JamesTwallin/gas_sensor/hardware/phone_board_mems/preview/phone_board_mems-F_Silkscreen.pdf

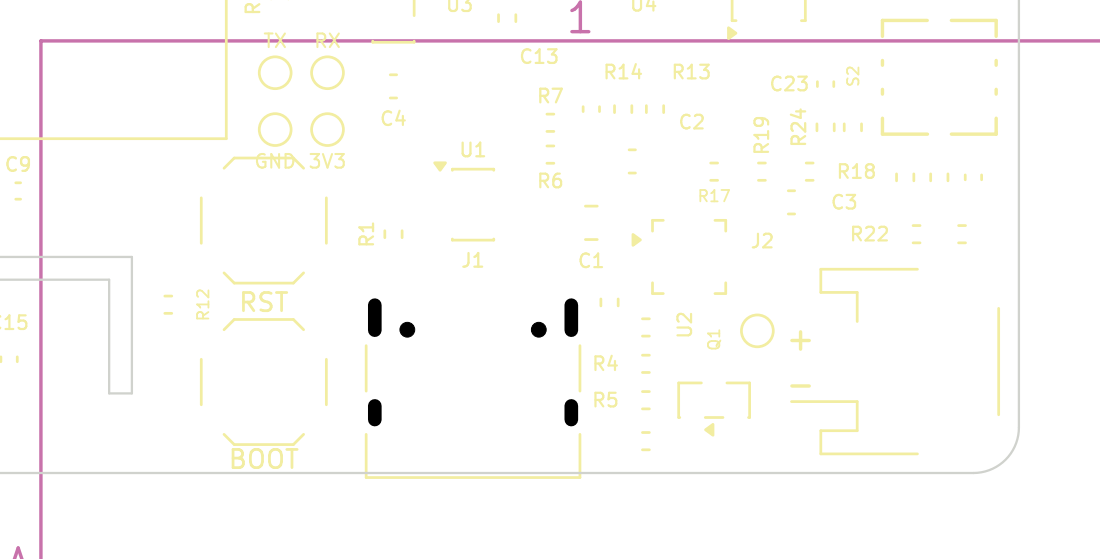
[picture p29: page 1]

Id: 5/7 Title: File: phone_board_mems.kicad_pcb Sheet:
