JamesTwallin/gas_sensor/hardware/phone_board_mems/preview/phone_board_mems-In1_Cu.pdf

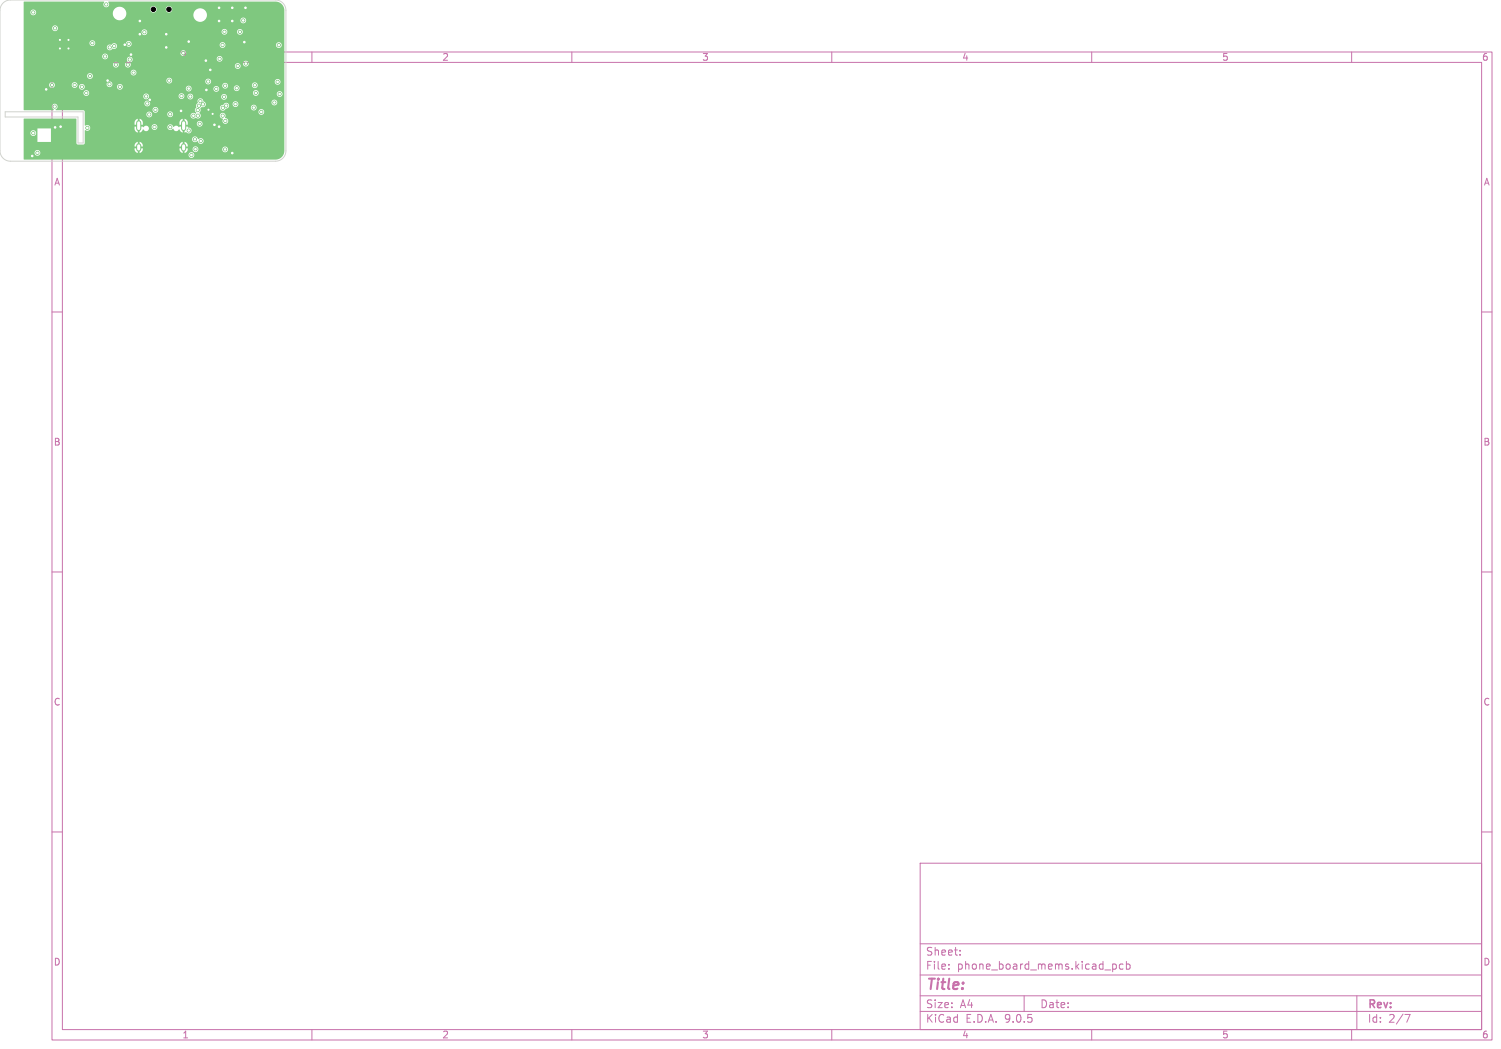
[picture p30: page 1]

Id: 2/7 Title: File: phone_board_mems.kicad_pcb Sheet:
