JamesTwallin/gas_sensor/hardware/phone_board_mems/preview/phone_board_mems-In2_Cu.pdf

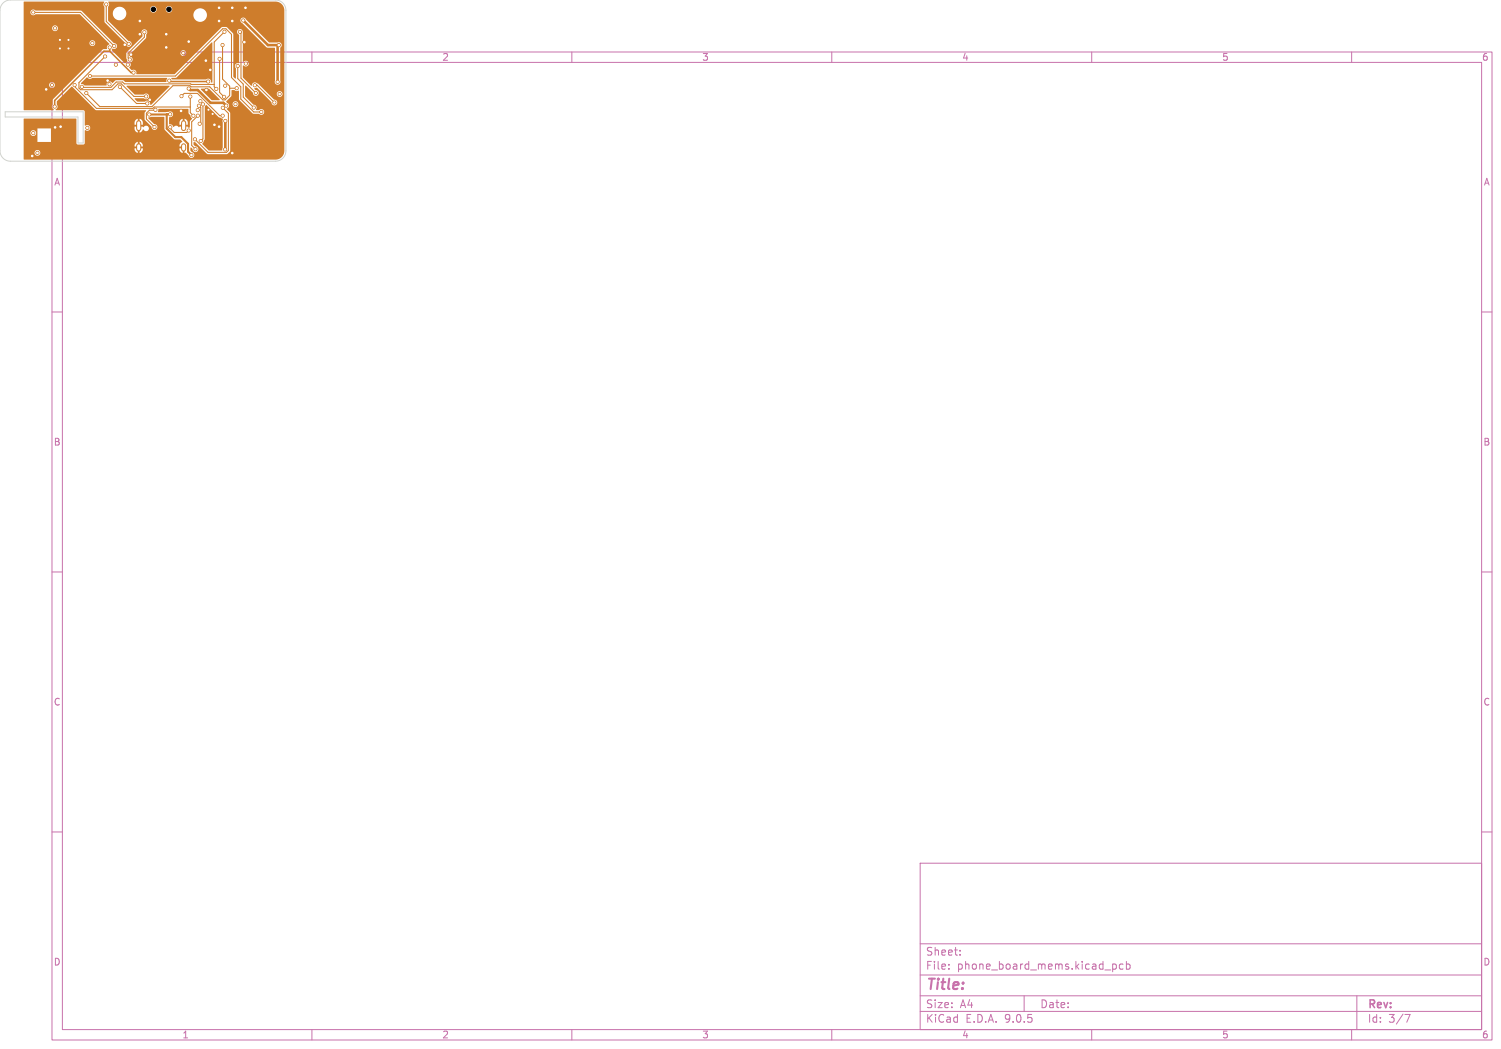
[picture p31: page 1]

Id: 3/7 Title: File: phone_board_mems.kicad_pcb Sheet:
