JamesTwallin/gas_sensor/hardware/phone_board_mems/preview/schematic.pdf

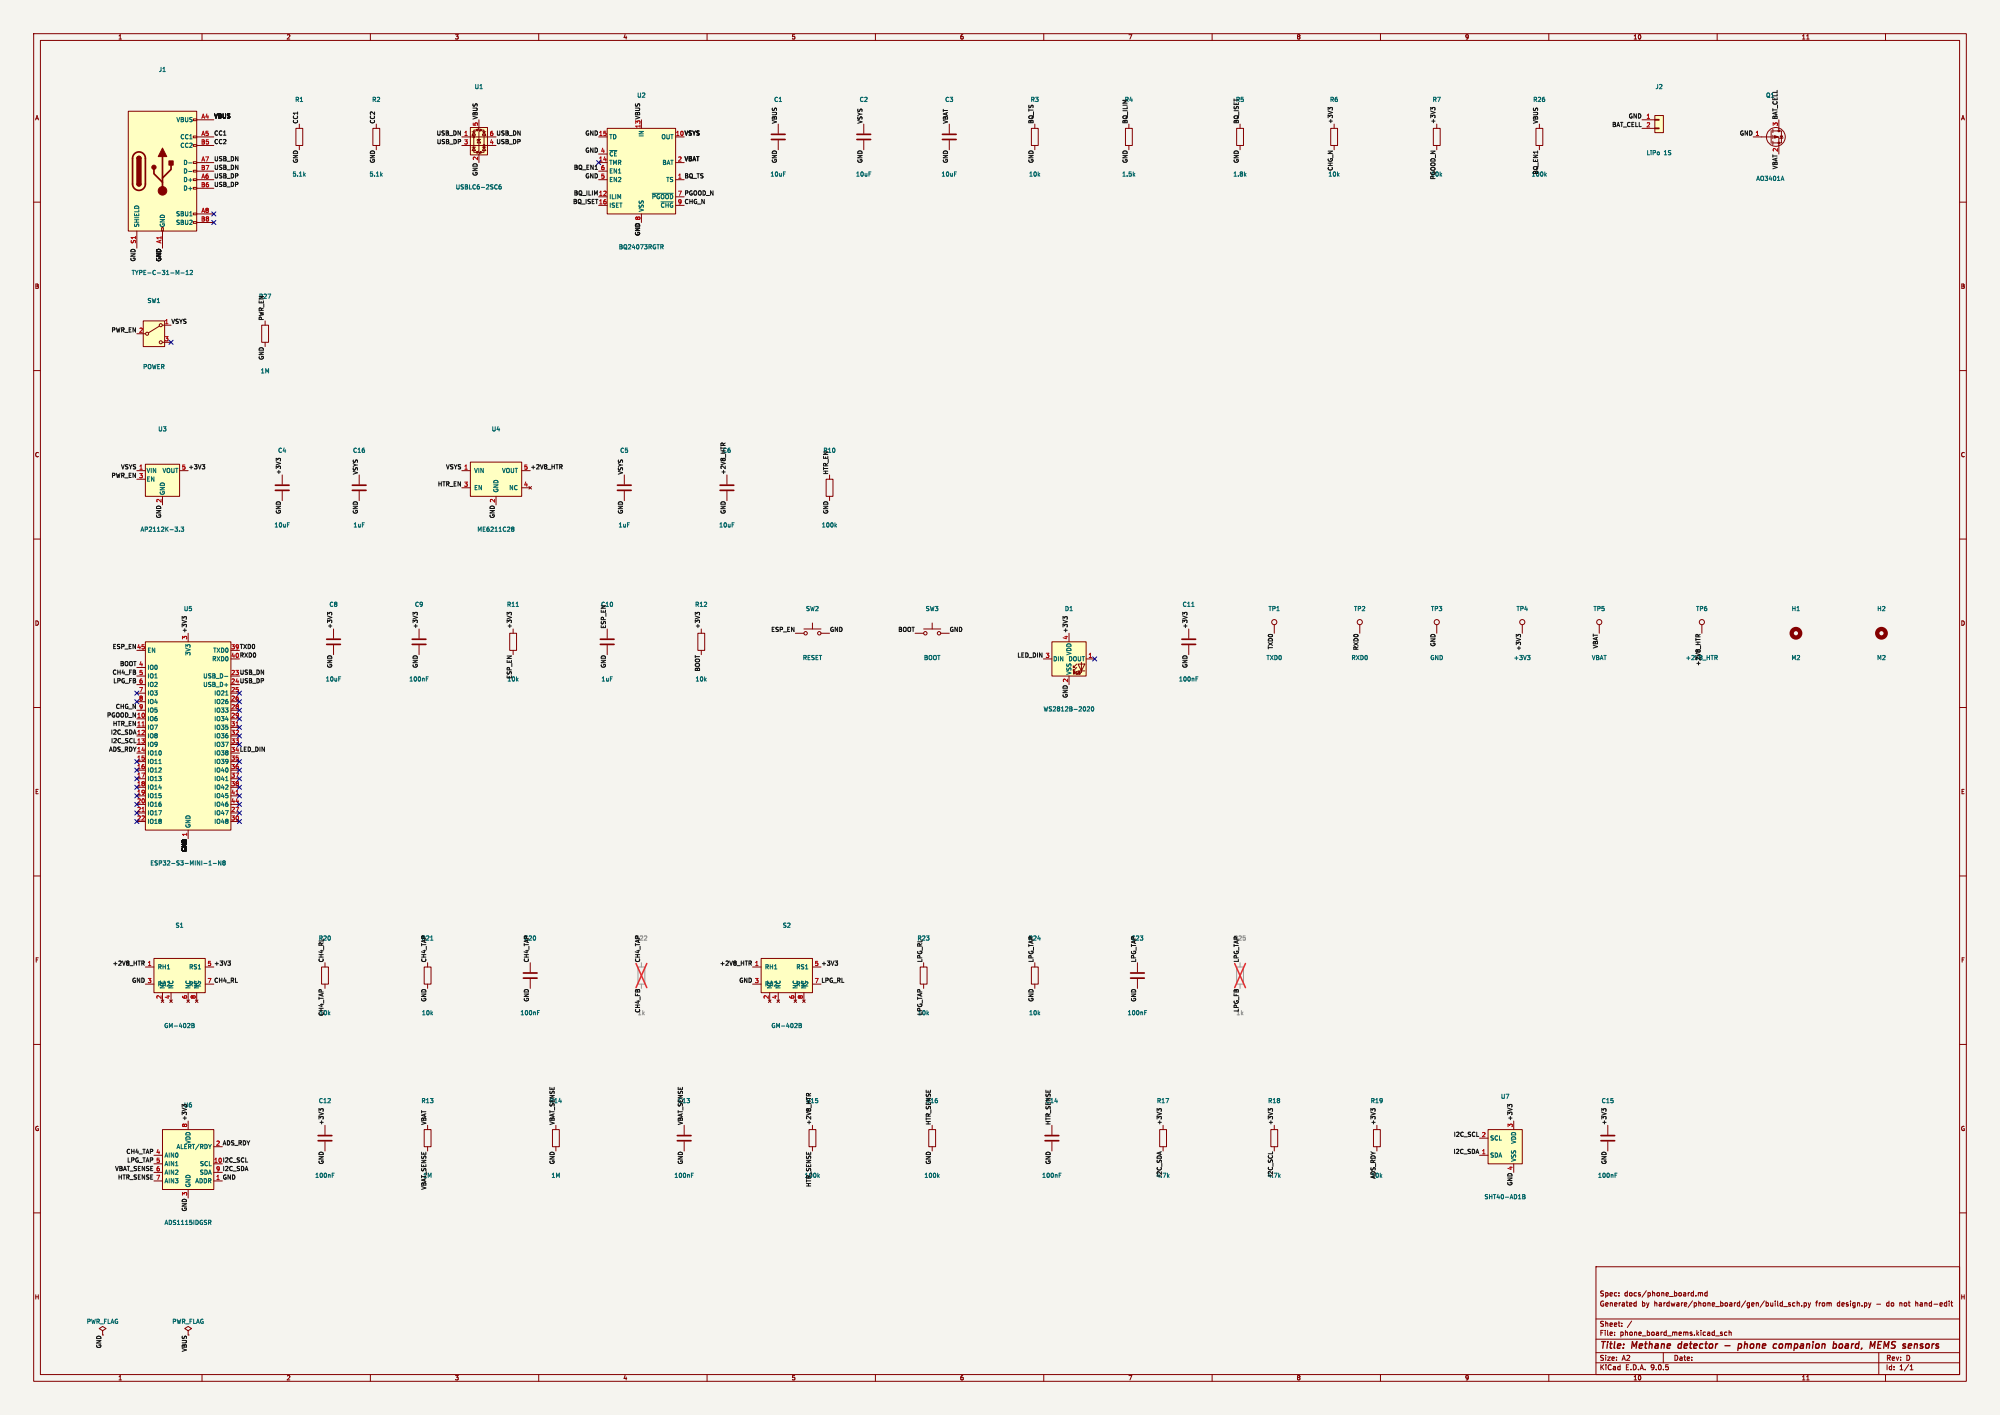
[picture p32: page 1]

8 OUT 10 BAT 2 TS 1 ~{PGOOD}7 ~{CHG}9 U2 BQ24073RGTR

3 ALERT/RDY 2 SCL 10 SDA 9 ADDR 1 U6 ADS1115IDGSR
GND +3V3 GND
